Workshop88/thotcon0x5/hardware/attic/iss_T1/fixes/B_copper.jpg

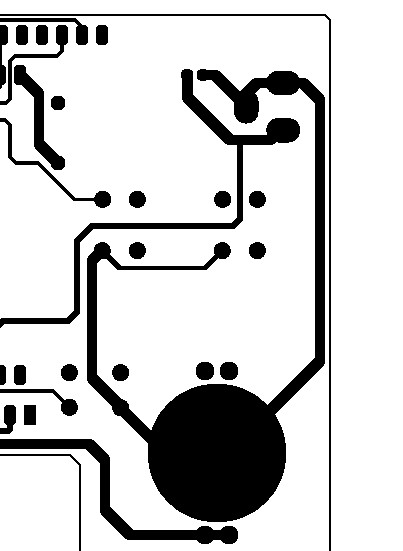
hardware/attic/iss_T1/fixes/B_copper.jpg
