Workshop88/thotcon0x5/hardware/attic/iss_T1/fixes/reset_1.jpg

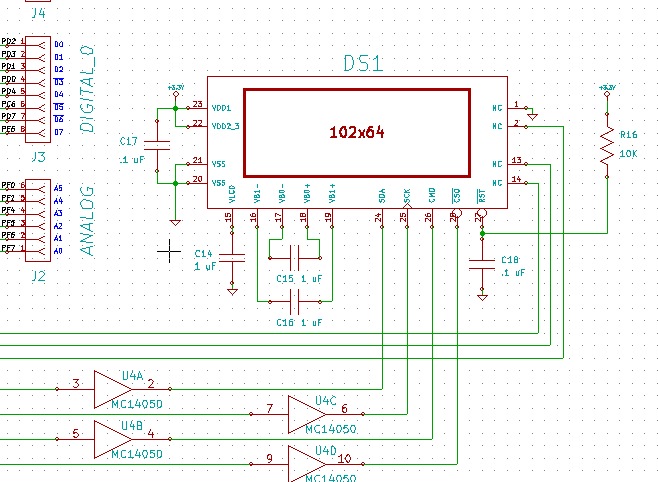
hardware/attic/iss_T1/fixes/reset_1.jpg
