Workshop88/thotcon0x5/hardware/development/iss_p1/release/thotcon_0x5_SCHEM-A.pdf

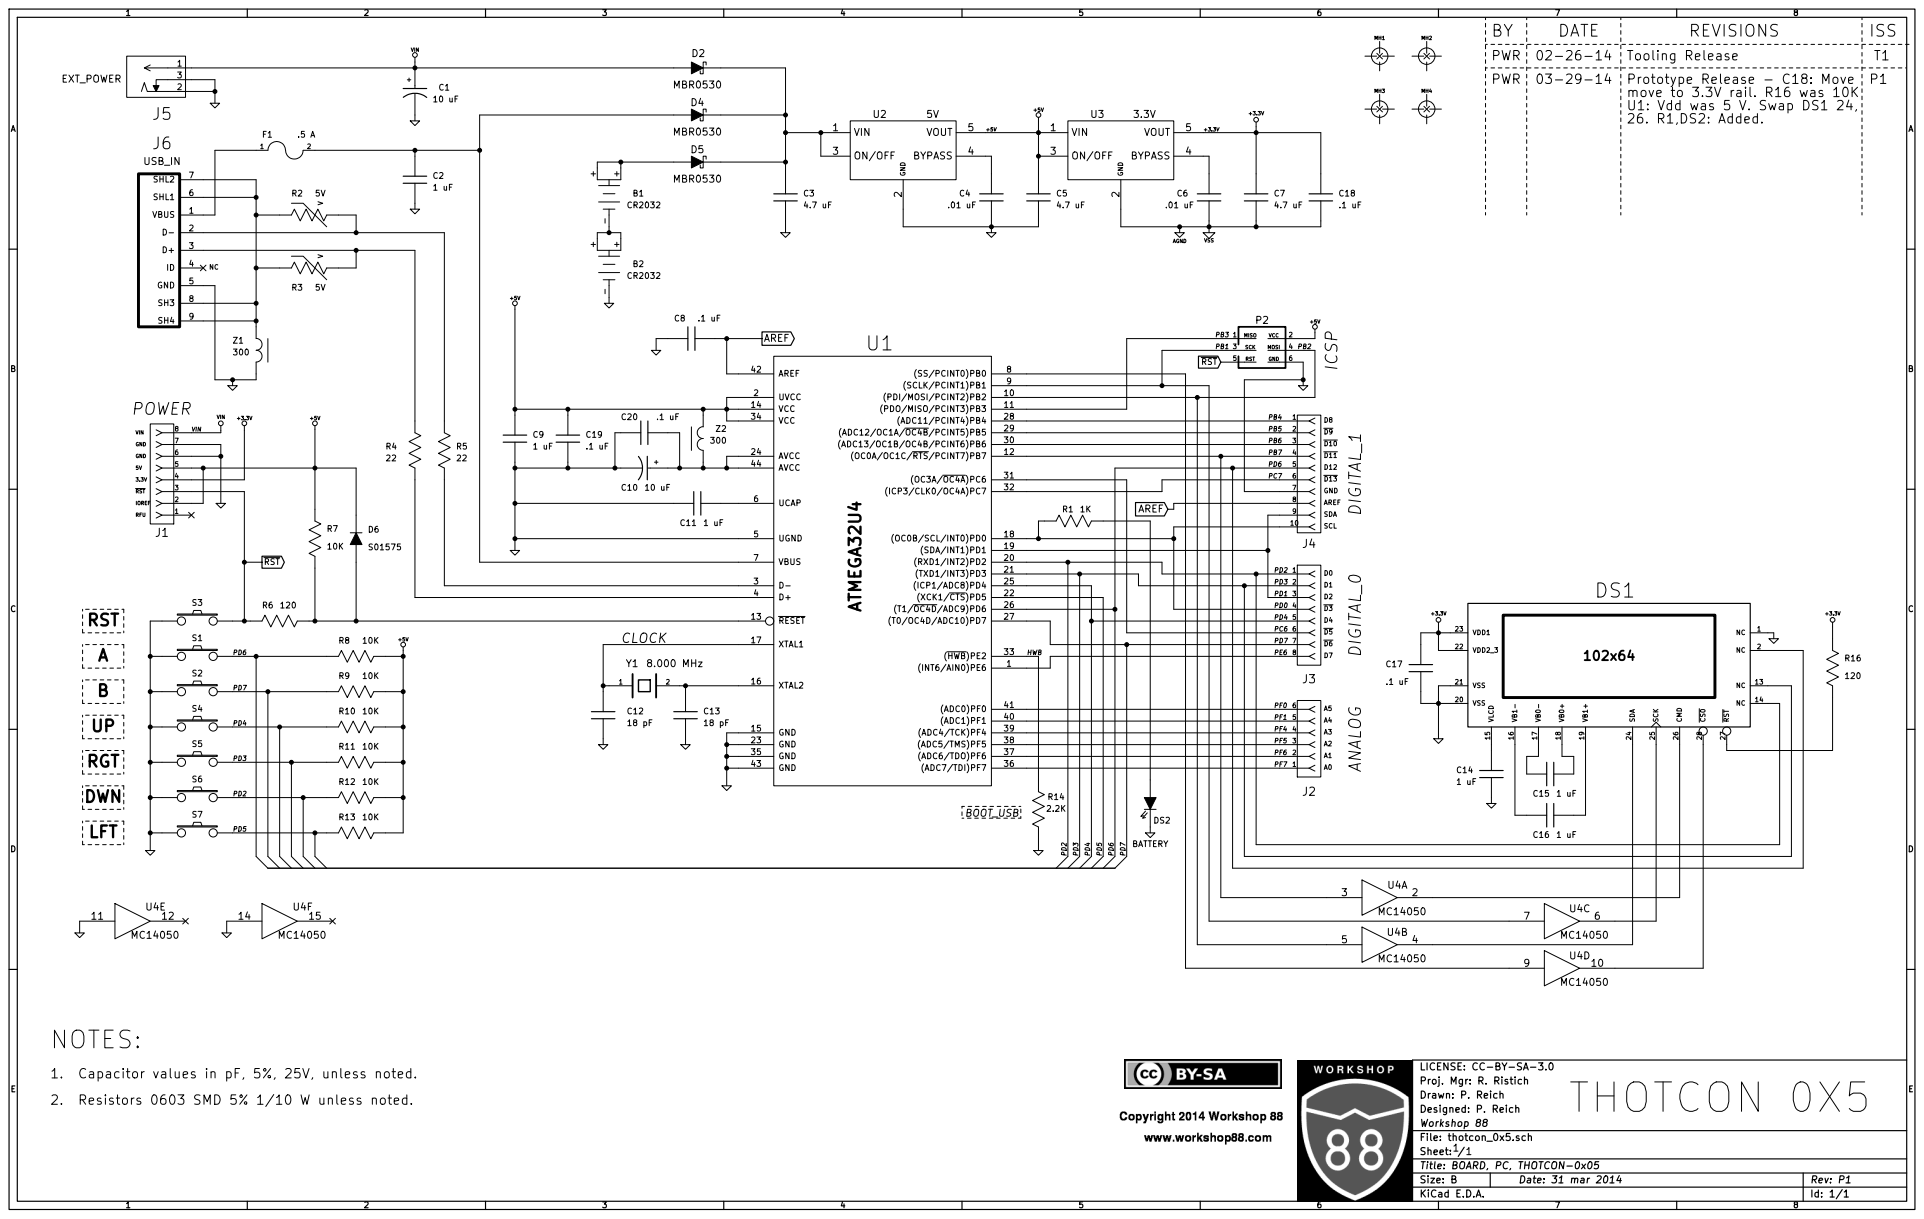
[picture p17: page 1]

120 Prototype Release - C18: Move P1 move to 3.3V rail. R16 was 10K U1: Vdd was 5 V. Swap DS1 24,

22 1. Capacitor values in pF, 5%, 25V, unless noted. 2. Resistors 0603 SMD 5% 1/10 W unless noted. NOTES:

LICENSE: CC-BY-SA-3.0
Id: 1/1 Title: BOARD, PC, THOTCON-0x05 File: thotcon_0x5.sch Sheet: / Workshop 88 Designed: P. Reich Drawn: P. Reich Proj. Mgr: R. Ristich
