Workshop88/thotcon0x5/hardware/development/iss_p1/release/thotcon_0x5_SCHEM-B.pdf

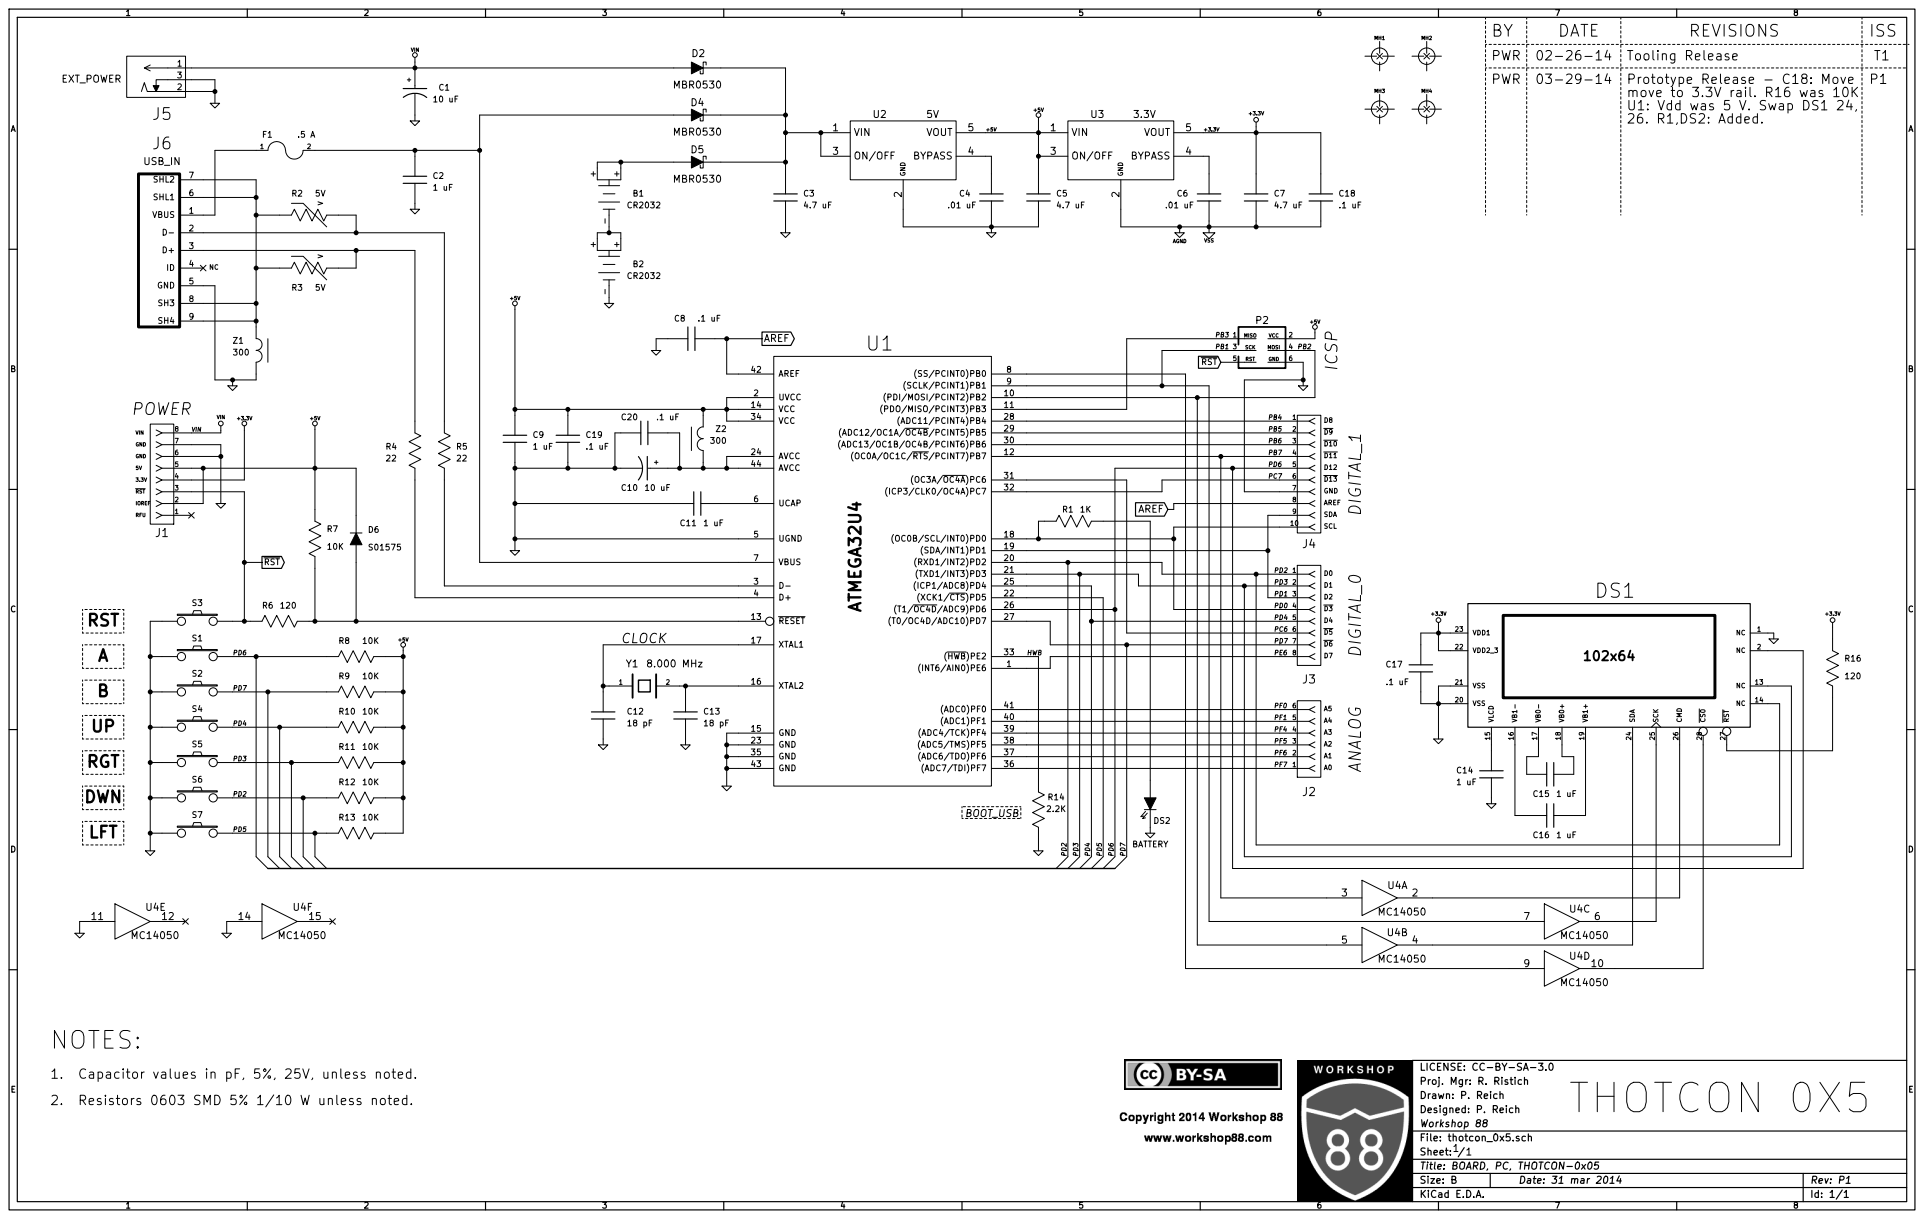
[picture p18: page 1]
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

22 1. Capacitor values in pF, 5%, 25V, unless noted.

LICENSE: CC-BY-SA-3.0
Designed: P. Reich Drawn: P. Reich Proj. Mgr: R. Ristich

2. Resistors 0603 SMD 5% 1/10 W unless noted.
