Workshop88/thotcon0x5/hardware/attic/iss_T1/release/thotcon_0x5-B_copper_MIRROR.pdf

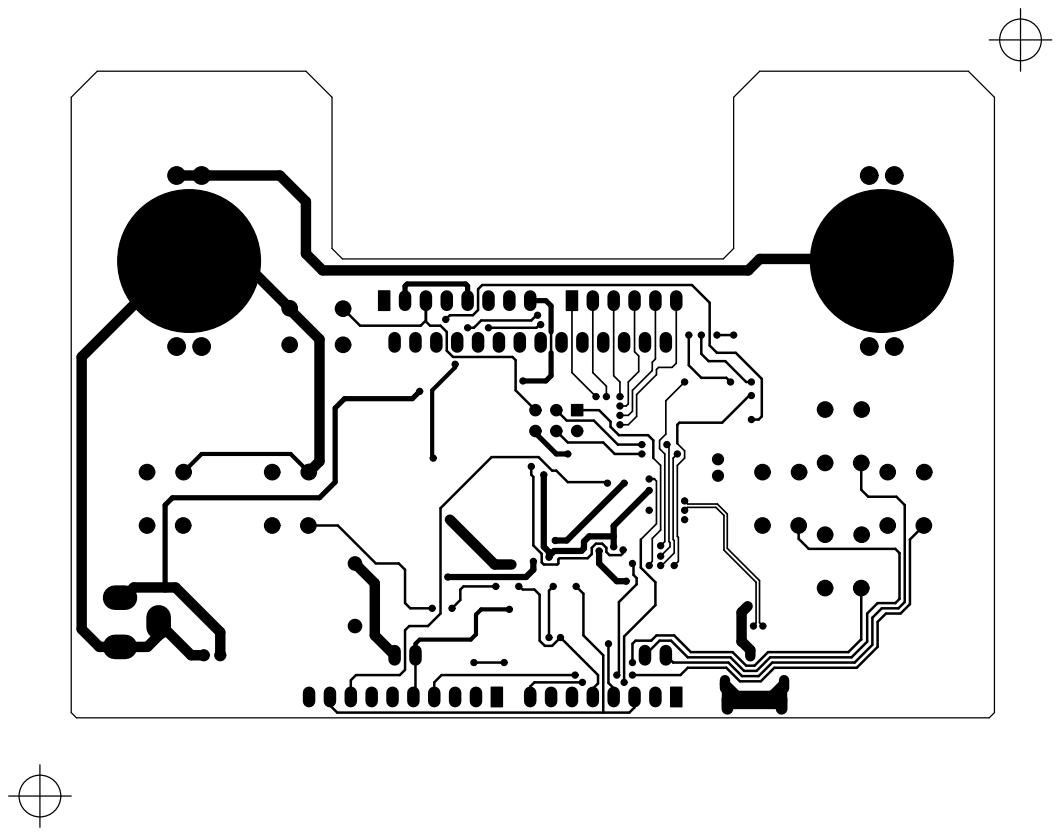
[picture p29: page 1]
