Workshop88/thotcon0x5/hardware/attic/iss_T1/release/thotcon_0x5-B_Mask.pdf

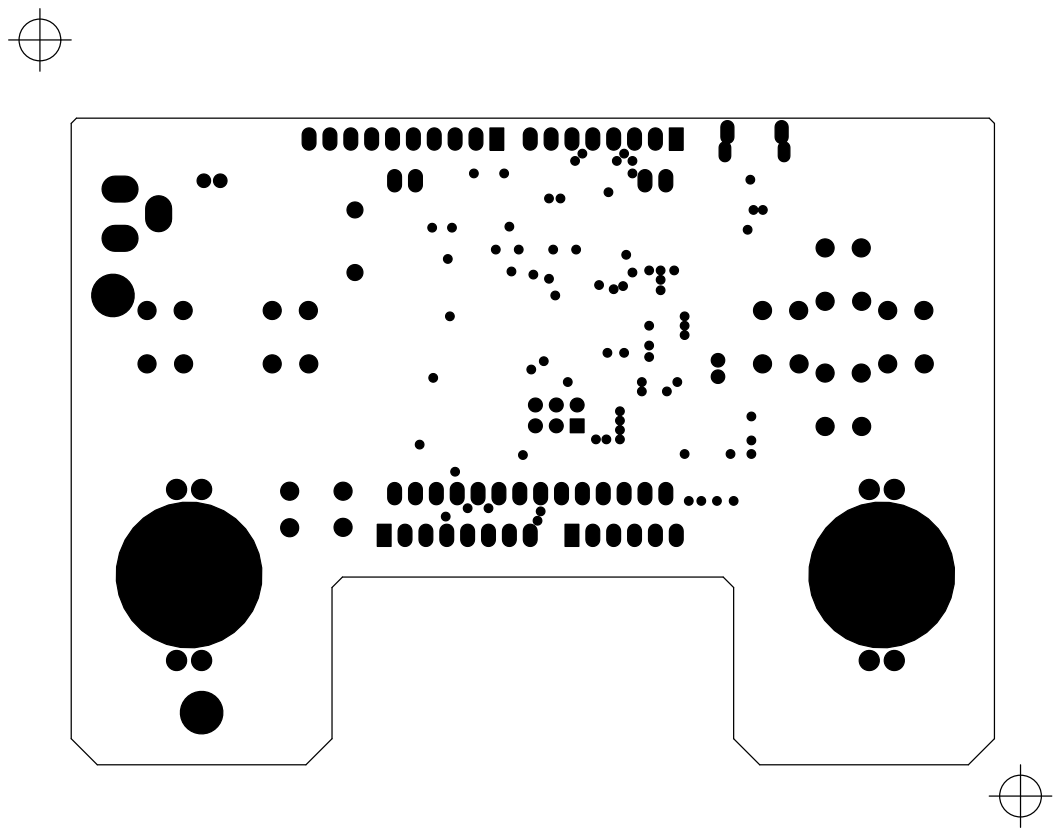
[picture p30: page 1]
