Workshop88/thotcon0x5/hardware/attic/iss_T1/release/thotcon_0x5-B_SilkS.pdf

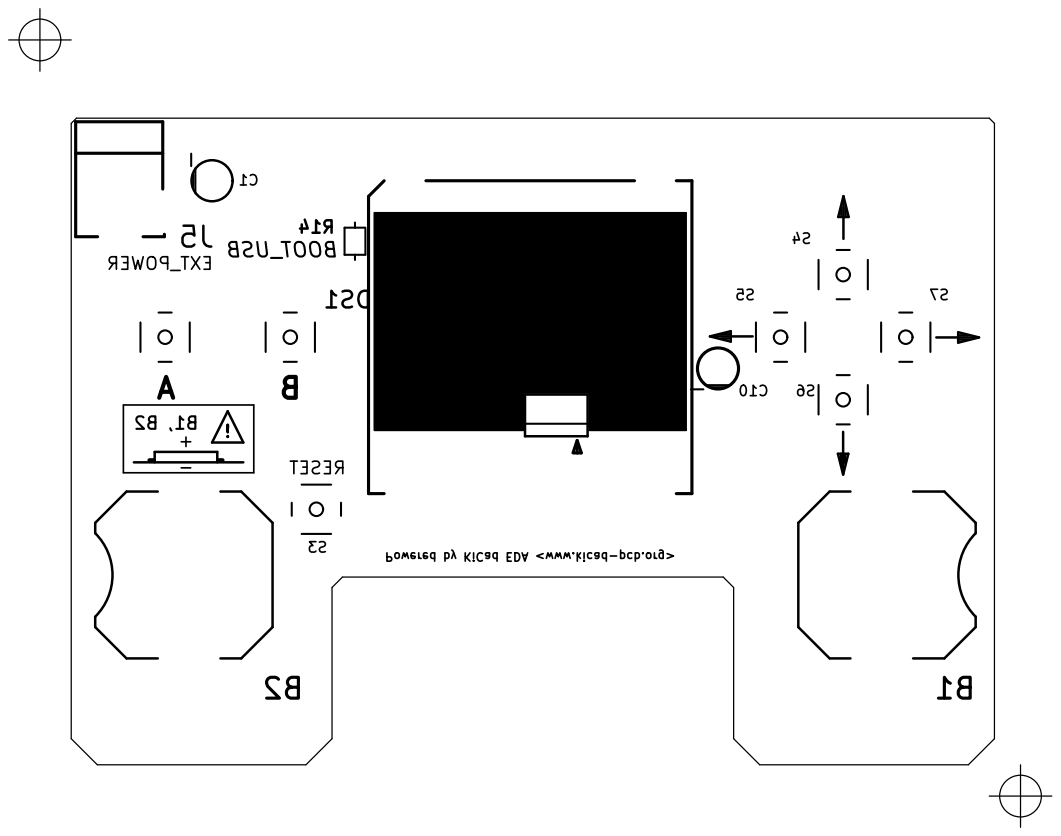
[picture p31: page 1]
