Workshop88/thotcon0x5/hardware/attic/iss_T1/release/thotcon_0x5-Dwgs_User.pdf

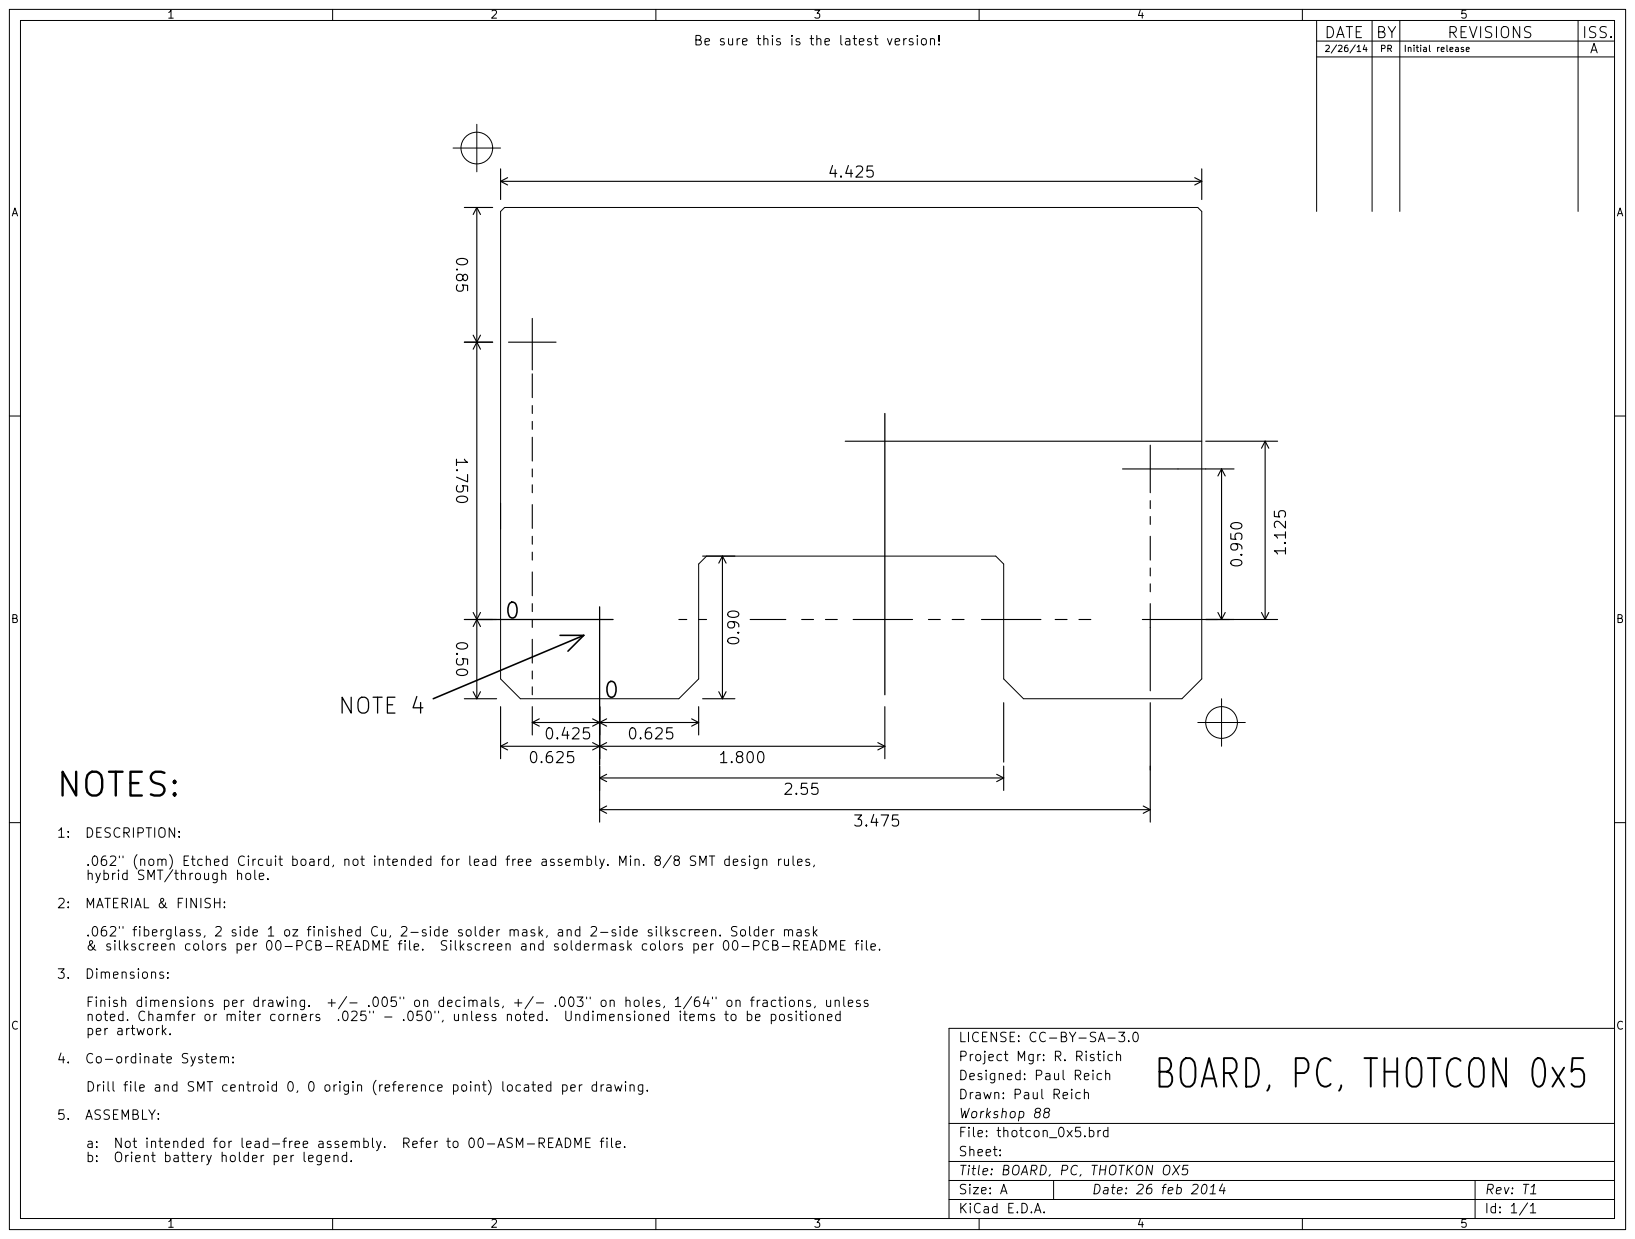
[picture p33: page 1]
