Workshop88/thotcon0x5/hardware/attic/iss_T1/release/thotcon_0x5-Edge_Cuts.pdf

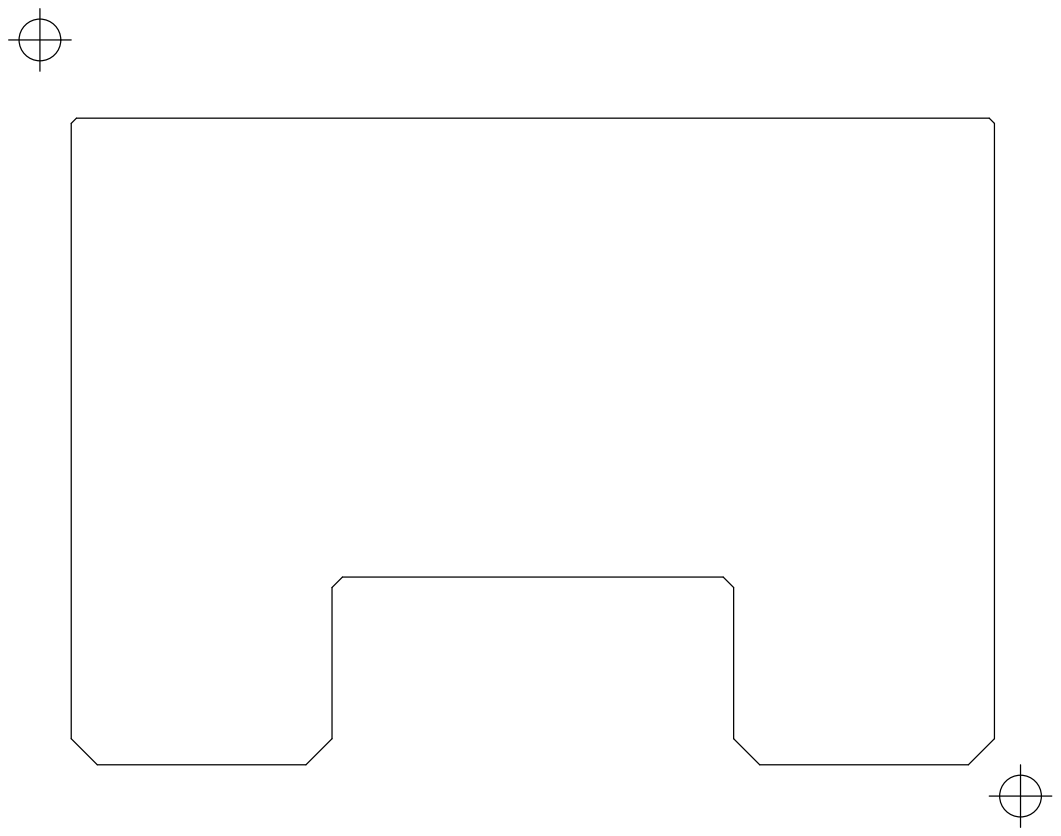
[picture p34: page 1]
