Workshop88/thotcon0x5/hardware/attic/iss_T1/release/thotcon_0x5-F_copper.pdf

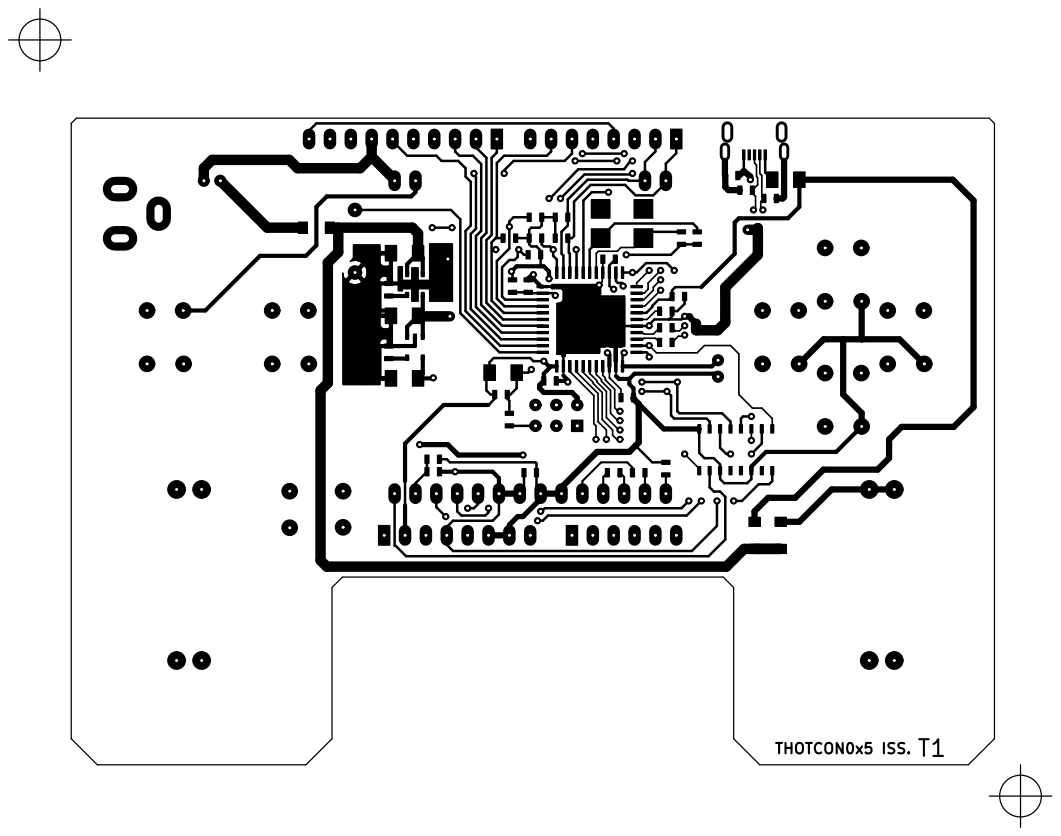
[picture p35: page 1]
