Workshop88/thotcon0x5/hardware/attic/iss_T1/release/thotcon_0x5_SCHEM_A.pdf

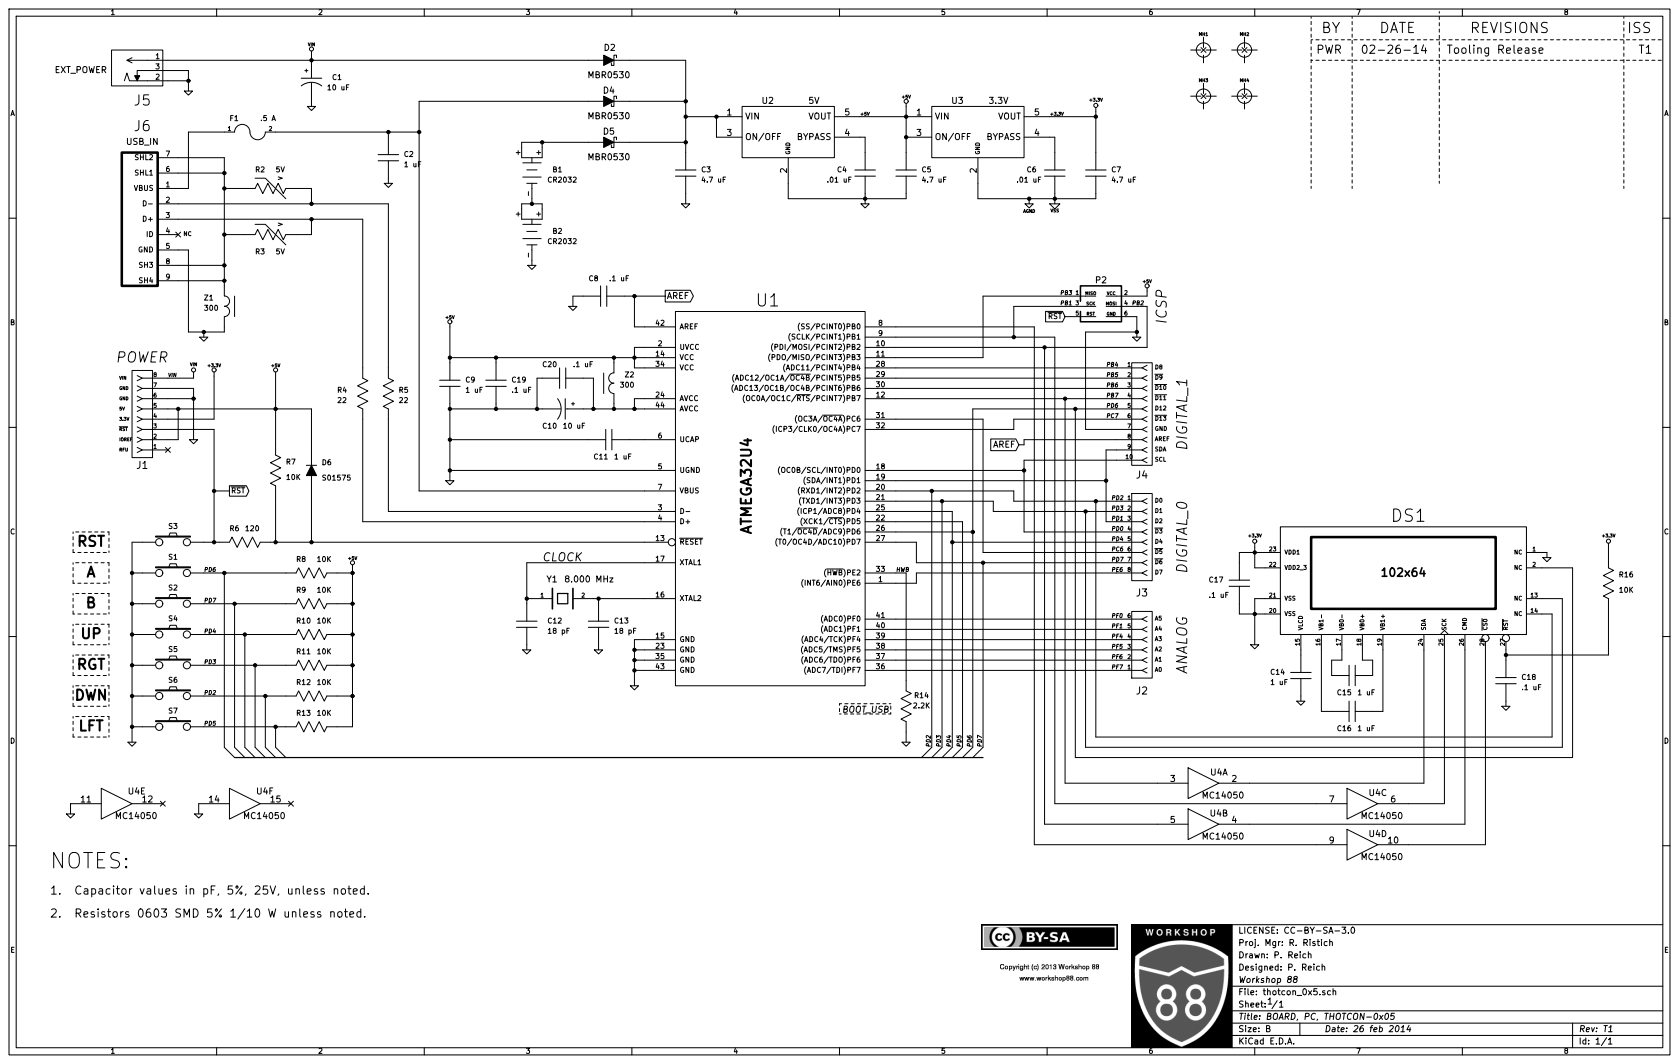
[picture p38: page 1]
