Workshop88/thotcon0x5/hardware/attic/iss_T1/thotcon_0x5.sch

## KiCad design hardware/attic/iss_T1/thotcon_0x5.sch (2014-03-19)

Schematic: thotcon_0x5.sch

Parts:
B1, B2: CR2032; SOCK_2032_THM; MFR_PN BAT-HLD-001-THM
C1, C10: 10 uF; DM5_RM2_THM; MFR_PN ECEA1VKA100
C2, C9, C11, C14, C15, C16: 1 uF; SM0603_Capa; MFR_PN GRM188R71E105KA12
C3, C5, C7: 4.7 uF; SM1206; MFR_PN GRM31CR71E475KA88L
C4, C6: .01 uF; SM0603_Capa; MFR_PN GRM188R71C103KA01D
C8, C17, C18, C19, C20: .1 uF; SM0603_Capa; MFR_PN GRM188R71H104KA93
C12, C13: 18 pF; SM0603_Capa; MFR_PN GRM1885C1H180JA01D
D2, D4, D5: MBR0530; MFR_PN MBR0530T1G
D6: S01575; SM1206POL; MFR_PN CD1206-S01575
DS1: EA_DOGS102; DOGS102; MFR_PN DOGS102W-6
F1: .5 A; SM1206; MFR_PN 1206L050/15YR
J1: POWER; SIL-8; MFR_PN M20-7820842
J2: ANALOG; SIL-6; MFR_PN M20-7820646
J3: DIGITAL_0; SIL-8; MFR_PN M20-7820842
J4: DIGITAL_1; SIL-10-MOD; MFR_PN M20-7821042
J5: EXT_POWER; JACK_PJ102; MFR_PN PJ-102A
J6: USB_IN; USB_MICRO_B_THM; MFR_PN 2040002-1
MH1, MH2, MH3, MH4: TOOLING; hole_5mm
P2: ICSP; pin_array_3x2
R2, R3: 5V; SM0603; MFR_PN CG0603MLC-05E
R4, R5: 22; SM0603; MFR_PN ERJ-3GEYJ220V
R6: 120; SM0603; MFR_PN ERJ-3GEYJ121V
R7, R8, R9, R10, R11, R12, R13, R16: 10K; SM0603; MFR_PN ERJ-3GEYJ103V
R14: 2.2K; RC05_300; MFR_PN CF18JT2K20
S1: A; PB_NO_6x6; MFR_PN B3F-1000
S2: B; PB_NO_6x6; MFR_PN B3F-1000
S3: RST; PB_NO_6x6; MFR_PN B3F-1000
S4: UP; PB_NO_6x6; MFR_PN B3F-1000
S5: RGT; PB_NO_6x6; MFR_PN B3F-1000
S6: DWN; PB_NO_6x6; MFR_PN B3F-1000
S7: LFT; PB_NO_6x6; MFR_PN B3F-1000
U1: ATMEGA32U4; TQFP44; MFR_PN ATMEGA32U4-AU
U2: 5V; SOT23-5; MFR_PN LP2985-50DBVR
U3: 3.3V; SOT23-5; MFR_PN LP2985-33DBVR
U4: MC14050; SO16E
Y1: 8.000 MHz; CRYSTAL_SMD_4824_4; MFR_PN ABC2-8.000MHZ-4-T
Z1, Z2: 300; SM0603; MFR_PN MMZ1608-B-301C

Notes on the sheet:
CLOCK
~D3~
~D5~
~D6~
~D9~
~D10~
~D11~
D12
~D13~
GND
AREF
1. Capacitor values in pF, 5%, 25V, unless noted. 2. Resistors 0603 SMD 5% 1/10 W unless noted.
NOTES:
VIN
3.3V
~RST~
BY DATE REVISIONS ISS
PWR 02-26-14 Tooling Release T1
BOOT_USB
IOREF
RFU
SDA
SCL
