Workshop88/thotcon0x5/hardware/attic/iss_T1/originals/thotcon_0x5.sch

## KiCad design hardware/attic/iss_T1/originals/thotcon_0x5.sch (2014-03-19)

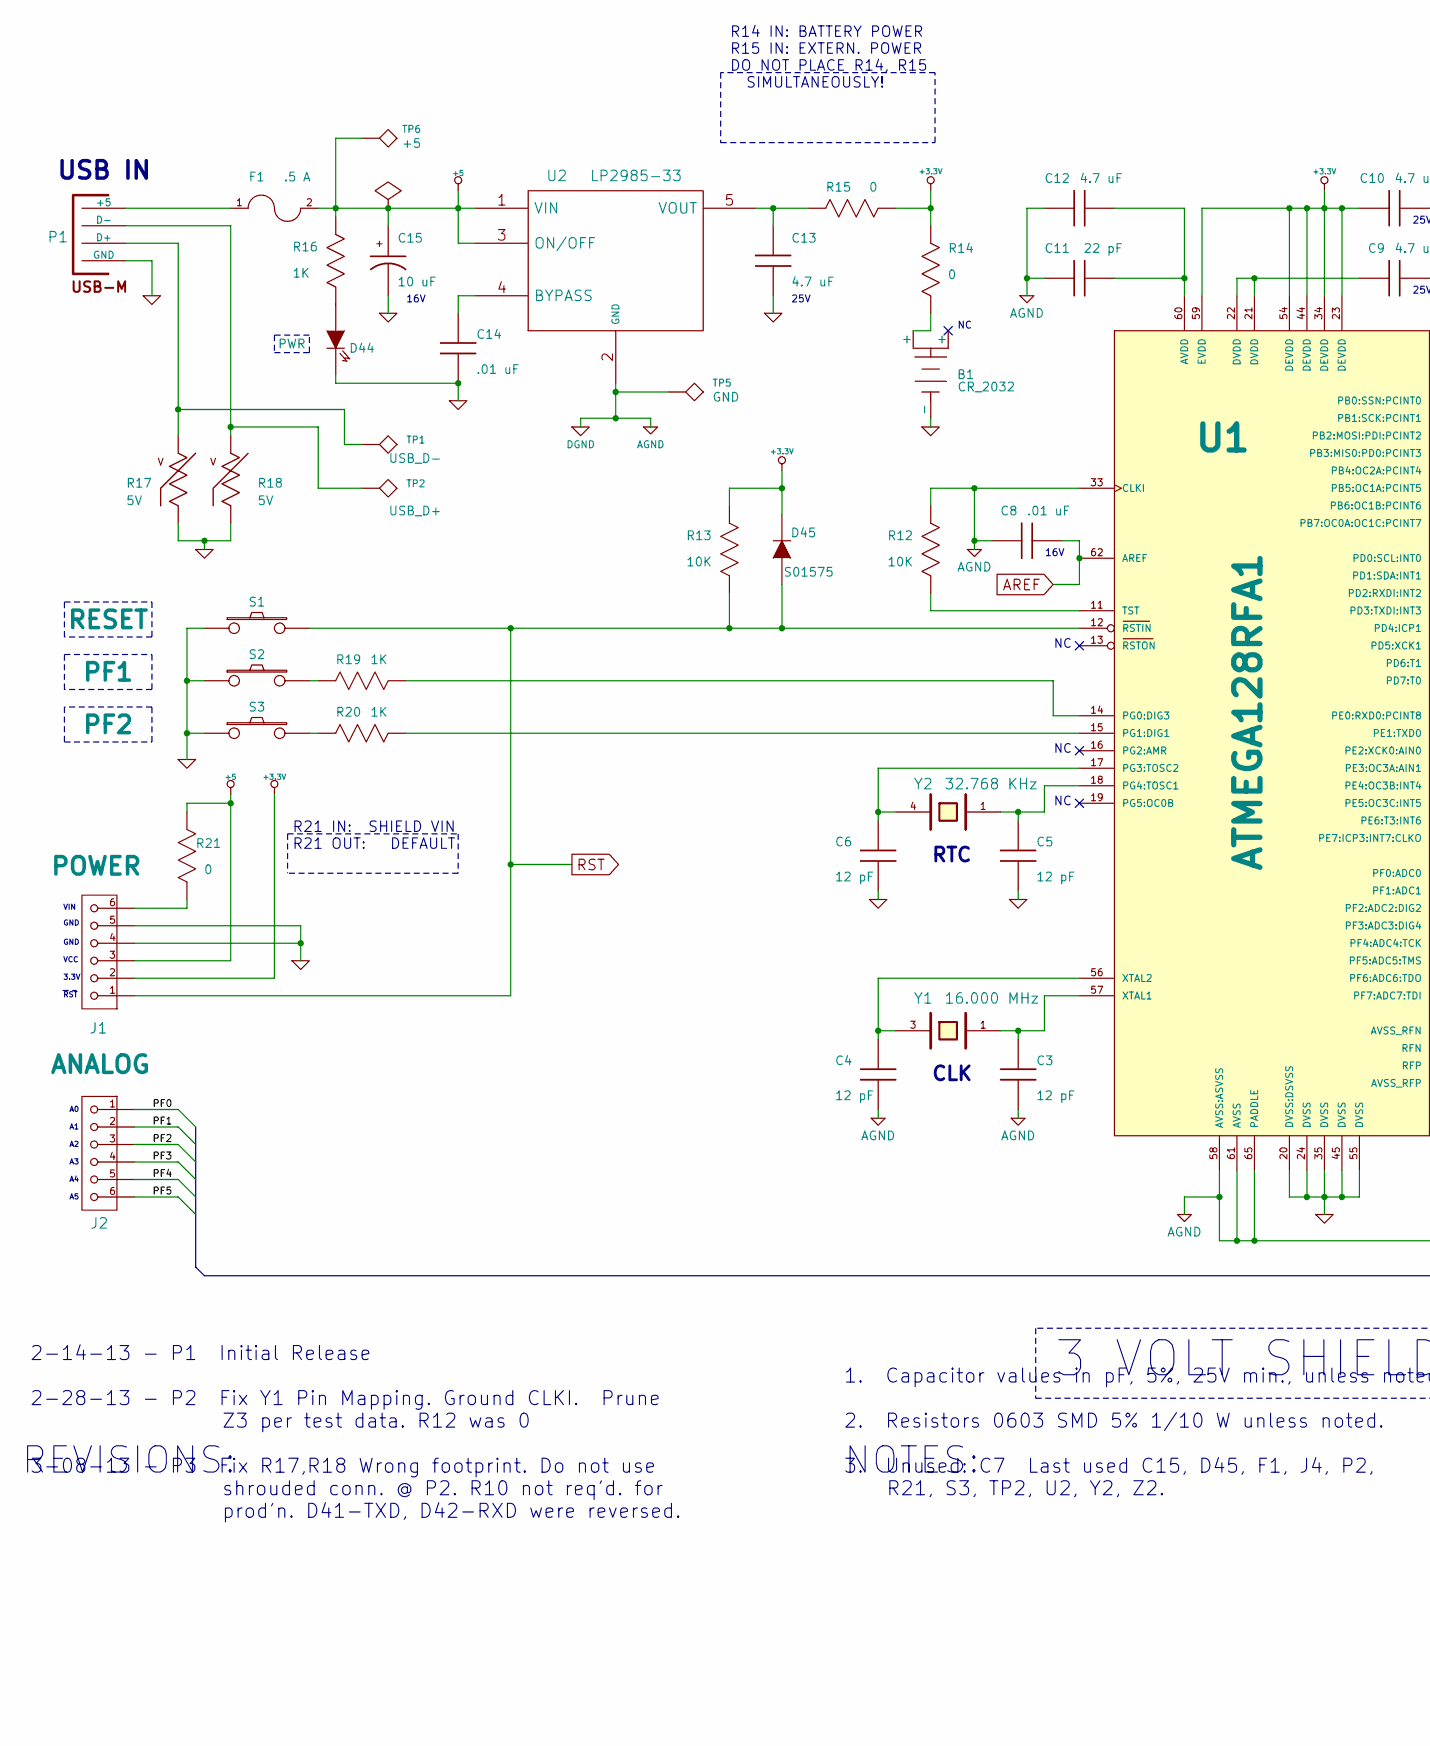
[picture p39: schematic thotcon_0x5.sch, part in row 1, column 1]

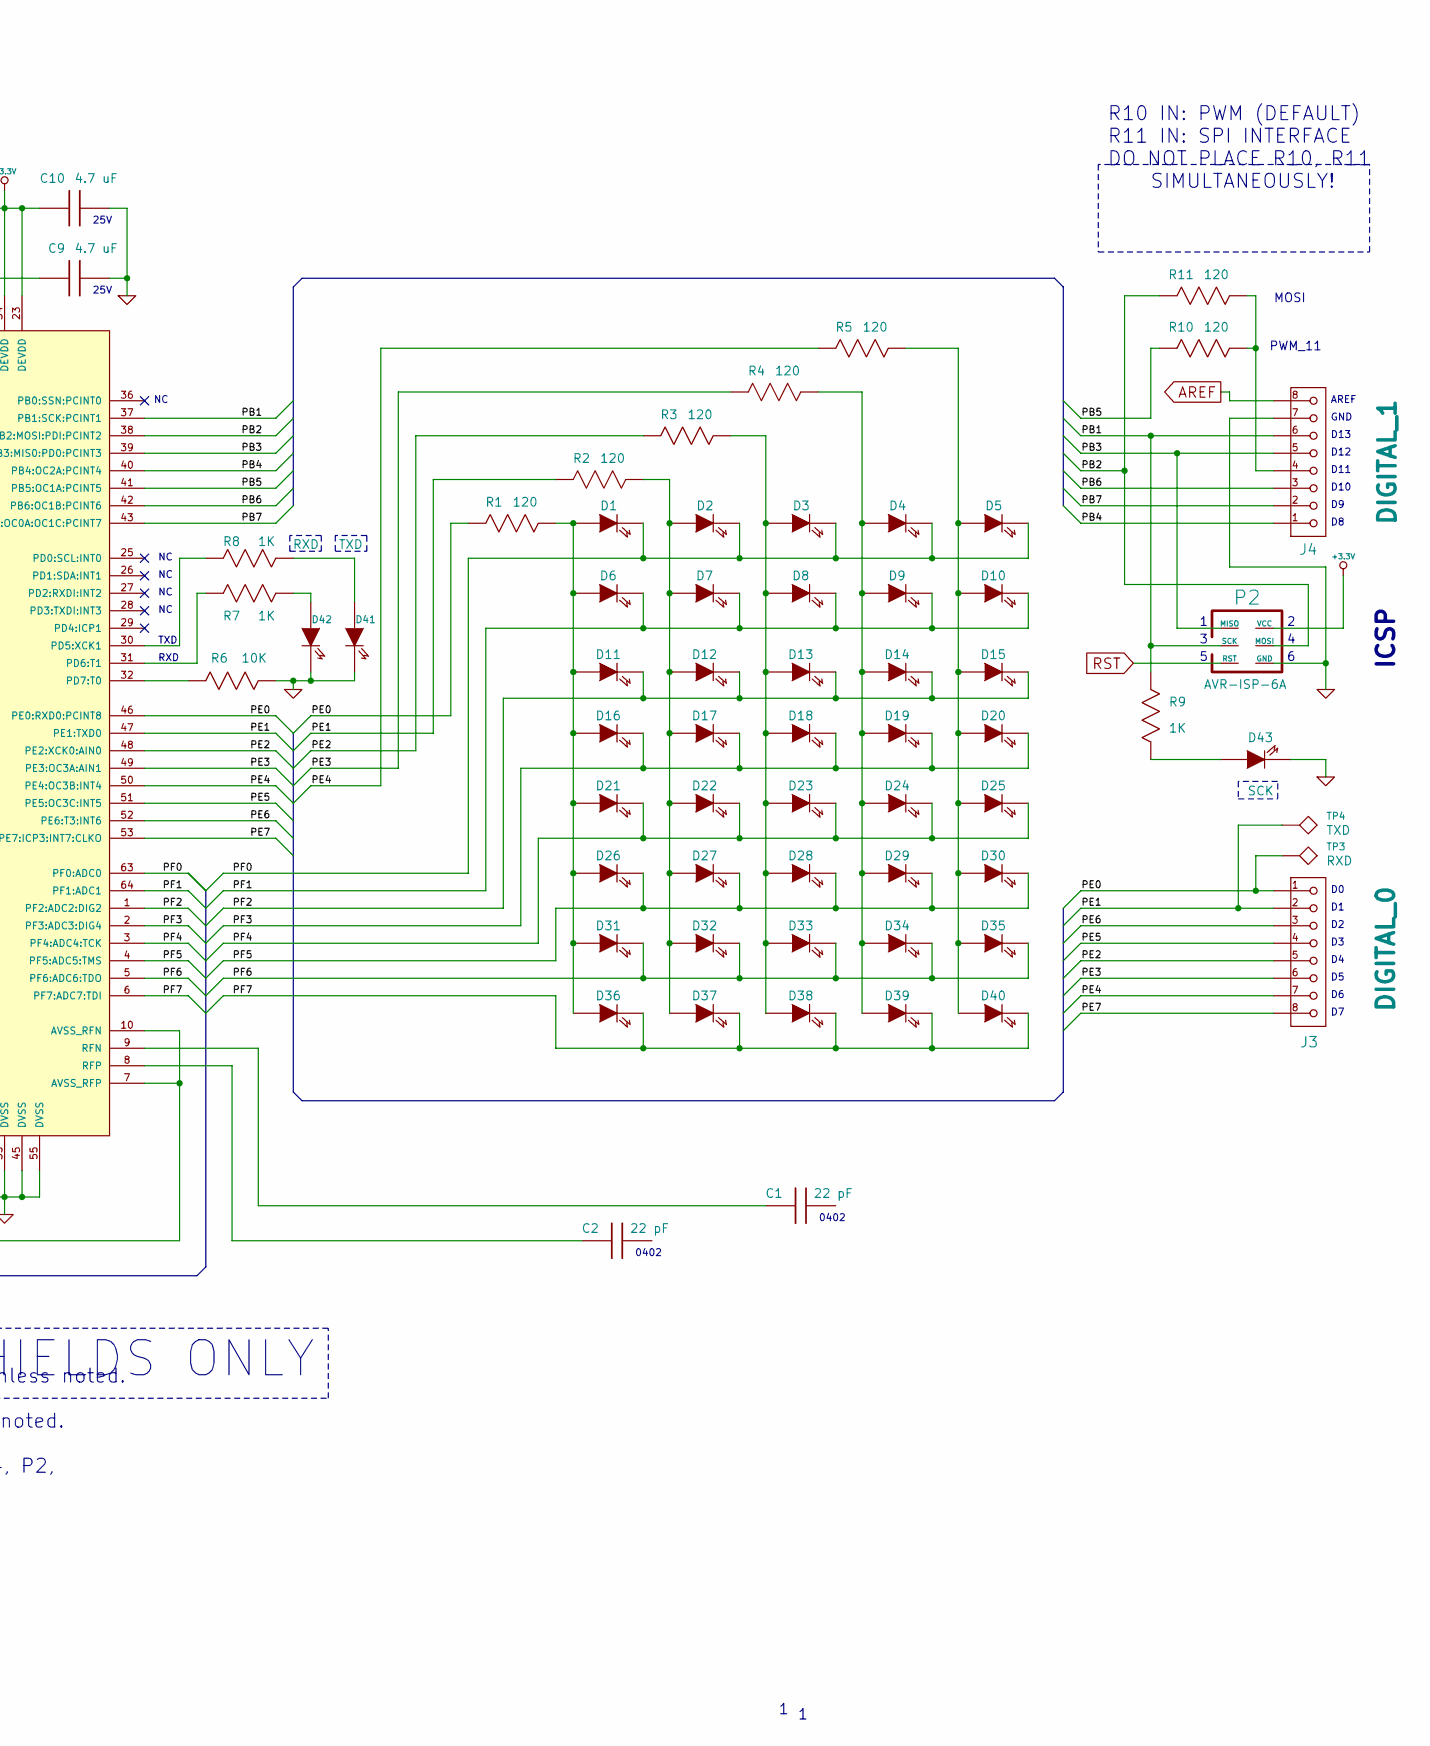
[picture p40: schematic thotcon_0x5.sch, part in row 1, column 2]

Parts:
B1: CR_2032; BAT_HLD_2032; MFR_PN BAT-HLD-001
C1, C2, C11: 22 pF; SM0402; MFR_PN 04023U220JAT2A
C3, C4, C5, C6: 12 pF; SM0603_Capa; MFR_PN GRM1885C1H120JA01D
C8, C14: .01 uF; SM0603_Capa; MFR_PN GRM188R71C103KA01D
C9, C10, C12, C13: 4.7 uF; SM1206; MFR_PN GRM31CR71E475KA88L
C15: 10 uF; c_elec_4x5.8; MFR_PN UWF1C100MCL1GB
D1, D2, D3, D4, D5, D6, D7, D8, D9, D10, D11, D12, D13, D14, D15, D16, D17, D18, D19, D20, D21, D22, D23, D24, D25, D26, D27, D28, D29, D30, D31, D32, D33, D34, D35, D36, D37, D38, D39, D40: RED; LED-1206; MFR_PN APTL3216SURCK
D41: TXD; LED-1206; MFR_PN APTL3216SURCK
D42: RXD; LED-1206; MFR_PN APTL3216SURCK
D43: SCK; LED-1206; MFR_PN APTL3216SURCK
D44: PWR; LED-1206; MFR_PN APTL3216SURCK
D45: S01575; SM1206POL; MFR_PN CD1206-S01575
F1: .5 A; SM1206; MFR_PN 1206L050/15YR
J1: POWER; SIL-6; MFR_PN M20-7820646
J2: ANALOG; SIL-6; MFR_PN M20-7820646
J3: DIGITAL_0; SIL-8; MFR_PN M20-7820842
J4: DIGITAL_1; SIL-8; MFR_PN M20-7820842
P1: USB_2_MALE; USB_A_PC_MALE
P2: AVR-ISP-6A; pin_array_3x2; MFR_PN 67996-406HLF
R1, R2, R3, R4, R5, R10, R11: 120; SM0603; MFR_PN ERJ-3GEYJ121V
R6, R12, R13: 10K; SM0603; MFR_PN ERJ-3GEYJ103V
R7, R8, R9, R16, R19, R20: 1K; SM0603; MFR_PN ERJ-3GEYJ102V
R14, R15, R21: 0; SM0603; MFR_PN ERJ-3GEY0R00V
R17, R18: 5V; SM0603; MFR_PN CG0603MLC-05E
S1: RESET; PB_NO_SMD_6x6R6; MFR_PN EVQQ2P02W
S2: PF1; PB_NO_SMD_6x6R6; MFR_PN EVQQ2R02W
S3: PF2; PB_NO_SMD_6x6R6; MFR_PN EVQQ2P02W
TP1: USB_D-; Measurement_Point_Round-TH_Small
TP2: USB_D+; Measurement_Point_Round-TH_Small
TP3: RXD; Measurement_Point_Round-TH_Small
TP4: TXD; Measurement_Point_Round-TH_Small
TP5: GND; Measurement_Point_Round-TH_Small
TP6: +5; Measurement_Point_Round-TH_Small
U1: ATMEGA128RFA1; MEGA128_QFN64; MFR_PN ATMEGA128RFA1-ZUR
U2: LP2985-33; SOT23-5; MFR_PN LP2985-33DBVR
Y1: 16.000 MHz; Crystal_SMD_0603_4Pads_RevA_09Aug2010; MFR_PN ABMM-16.000MHZ-B2-T
Y2: 32.768 KHz; CRYSTAL_SMD_2820_4; MFR_PN ECS-.327-12.5-17X-TR

Connections:
+3.3V: C10.1, D45.2 (K), J1.2, P2.2 (VCC), R13.1, R14.2, R15.2, U1.23 (DEVDD), U1.34 (DEVDD), U1.44 (DEVDD), U1.54 (DEVDD), U1.59 (EVDD)
+5: C15.1, F1.2, J1.3, R16.1, R21.2, TP6.1, U2.1 (VIN), U2.3 (ON/OFF)
AGND: B1.3 (-), C3.2, C4.2, C5.2, C6.2, C8.1, C9.2, C10.2, C11.1, C12.1, C13.2, C14.2, C15.2, D41.2 (K), D42.2 (K), D43.2 (K), D44.2 (K), J1.4, J1.5, J4.7, P1.4 (GND), P2.6 (GND), R6.1, R12.1, R17.2, R18.2, S1.1, S2.1, S3.1, TP5.1, U1.7 (AVSS_RFP), U1.10 (AVSS_RFN), U1.20 (DVSS:DSVSS), U1.24 (DVSS), U1.33 (CLKI), U1.35 (DVSS), U1.45 (DVSS), U1.55 (DVSS), U1.58 (AVSS:ASVSS), U1.61 (AVSS), U1.65 (PADDLE), U2.2 (GND)
AREF: C8.2, J4.8, U1.62 (AREF)
unnamed: B1.1 (+), R14.1
unnamed: C1.1, U1.9 (RFN)
unnamed: C2.1, U1.8 (RFP)
unnamed: C3.1, U1.57 (XTAL1), Y1.1
unnamed: C4.1, U1.56 (XTAL2), Y1.3
unnamed: C5.1, U1.18 (PG4:TOSC1), Y2.1
unnamed: C6.1, U1.17 (PG3:TOSC2), Y2.4
unnamed: C9.1, U1.21 (DVDD), U1.22 (DVDD)
unnamed: C11.2, C12.2, U1.60 (AVDD)
unnamed: C13.1, R15.1, U2.5 (VOUT)
unnamed: C14.1, U2.4 (BYPASS)
unnamed: D1.1 (A), D6.1 (A), D11.1 (A), D16.1 (A), D21.1 (A), D26.1 (A), D31.1 (A), D36.1 (A), R1.2
unnamed: D5.1 (A), D10.1 (A), D15.1 (A), D20.1 (A), D25.1 (A), D30.1 (A), D35.1 (A), D40.1 (A), R5.2
unnamed: D2.1 (A), D7.1 (A), D12.1 (A), D17.1 (A), D22.1 (A), D27.1 (A), D32.1 (A), D37.1 (A), R2.2
unnamed: D3.1 (A), D8.1 (A), D13.1 (A), D18.1 (A), D23.1 (A), D28.1 (A), D33.1 (A), D38.1 (A), R3.2
unnamed: D4.1 (A), D9.1 (A), D14.1 (A), D19.1 (A), D24.1 (A), D29.1 (A), D34.1 (A), D39.1 (A), R4.2
unnamed: D41.1 (A), R8.2
unnamed: D42.1 (A), R7.2
unnamed: D43.1 (A), R9.2
unnamed: D44.1 (A), R16.2
unnamed: F1.1, P1.1 (+5)
unnamed: J1.6, R21.1
unnamed: J4.4, R10.2, R11.2
unnamed: P1.2 (D-), R18.1, TP2.1
unnamed: P1.3 (D+), R17.1, TP1.1
unnamed: R6.2, U1.32 (PD7:T0)
unnamed: R7.1, U1.31 (PD6:T1)
unnamed: R8.1, U1.30 (PD5:XCK1)
unnamed: R12.2, U1.11 (TST)
unnamed: R19.1, S2.2
unnamed: R19.2, U1.14 (PG0:DIG3)
unnamed: R20.1, S3.2
unnamed: R20.2, U1.15 (PG1:DIG1)
PB1: J4.6, P2.3 (SCK), R9.1, U1.37 (PB1:SCK:PCINT1)
PB2: P2.4 (MOSI), R11.1, U1.38 (PB2:MOSI:PDI:PCINT2)
PB3: J4.5, P2.1 (MISO), U1.39 (PB3:MIS0:PD0:PCINT3)
PB4: J4.1, U1.40 (PB4:OC2A:PCINT4)
PB5: R10.1, U1.41 (PB5:OC1A:PCINT5)
PB6: J4.3, U1.42 (PB6:OC1B:PCINT6)
PB7: J4.2, U1.43 (PB7:OC0A:OC1C:PCINT7)
PE0: J3.1, R1.1, TP3.1, U1.46 (PE0:RXD0:PCINT8)
PE1: J3.2, R2.1, TP4.1, U1.47 (PE1:TXD0)
PE2: J3.5, R3.1, U1.48 (PE2:XCK0:AIN0)
PE3: J3.6, R4.1, U1.49 (PE3:OC3A:AIN1)
PE4: J3.7, R5.1, U1.50 (PE4:OC3B:INT4)
PE5: J3.4, U1.51 (PE5:OC3C:INT5)
PE6: J3.3, U1.52 (PE6:T3:INT6)
PE7: J3.8, U1.53 (PE7:ICP3:INT7:CLKO)
PF0: D1.2 (K), D2.2 (K), D3.2 (K), D4.2 (K), D5.2 (K), J2.1, U1.63 (PF0:ADC0)
PF1: D6.2 (K), D7.2 (K), D8.2 (K), D9.2 (K), D10.2 (K), J2.2, U1.64 (PF1:ADC1)
PF2: D11.2 (K), D12.2 (K), D13.2 (K), D14.2 (K), D15.2 (K), J2.3, U1.1 (PF2:ADC2:DIG2)
PF3: D16.2 (K), D17.2 (K), D18.2 (K), D19.2 (K), D20.2 (K), J2.4, U1.2 (PF3:ADC3:DIG4)
PF4: D21.2 (K), D22.2 (K), D23.2 (K), D24.2 (K), D25.2 (K), J2.5, U1.3 (PF4:ADC4:TCK)
PF5: D26.2 (K), D27.2 (K), D28.2 (K), D29.2 (K), D30.2 (K), J2.6, U1.4 (PF5:ADC5:TMS)
PF6: D31.2 (K), D32.2 (K), D33.2 (K), D34.2 (K), D35.2 (K), U1.5 (PF6:ADC6:TDO)
PF7: D36.2 (K), D37.2 (K), D38.2 (K), D39.2 (K), D40.2 (K), U1.6 (PF7:ADC7:TDI)
RST: D45.1 (A), J1.1, P2.5 (RST), R13.2, S1.2, U1.12 (RSTIN)

Notes on the sheet:
RTC
ICSP
USB IN
CLK
D10
D11
D12
D13
GND
AREF
R10 IN: PWM (DEFAULT) R11 IN: SPI INTERFACE DO NOT PLACE R10, R11 SIMULTANEOUSLY!
PWM_11
RXD
TXD
MOSI
1. Capacitor values in pF, 5%, 25V min., unless noted. 2. Resistors 0603 SMD 5% 1/10 W unless noted. 3. Unused: C7 Last used C15, D45, F1, J4, P2, R21, S3, TP2, U2, Y2, Z2.
NOTES:
16V
25V
0402
R14 IN: BATTERY POWER R15 IN: EXTERN. POWER DO NOT PLACE R14, R15 SIMULTANEOUSLY!
R21 IN: SHIELD VIN R21 OUT: DEFAULT
VIN
VCC
3.3V
RST
3 VOLT SHIELDS ONLY
REVISIONS:
2-14-13 - P1 Initial Release 2-28-13 - P2 Fix Y1 Pin Mapping. Ground CLKI. Prune Z3 per test data. R12 was 0 3-08-13 - P3 Fix R17,R18 Wrong footprint. Do not use shrouded conn. @ P2. R10 not req'd. for prod'n. D41-TXD, D42-RXD were reversed.
